GWan1234/openups/src/bms.cpp

#include "bms.h"
#include "bms_ncm.h"
#include "bms_lfp.h"
#include <Arduino.h>
#include <math.h>
#include <Preferences.h>
#include <SPIFFS.h>
#include "event_bus.h"
#include "time_utils.h"
#include "debug.h"

// 定义并初始化静态指针
BMS* BMS::instancePtr = nullptr;

BMS::BMS(I2CInterface& i2c_interface, const BMS_Config_t& config)
    : bq76920_(i2c_interface), config_(config), initialized_(false), available_(true),
      discharge_enabled_(false), charge_enabled_(false), i2c_failure_count_(0), i2c_power_enabled_(false),
      last_fast_update_(0), last_medium_update_(0), last_slow_update_(0), last_cc_update_(0),
      last_periodic_update_(0), last_day_update_(0), current_remaining_capacity(0.0f),
      accumulated_charge_mAh(0.0f), accumulated_discharge_mAh(0.0f),
      cc_ready_pending_(false), soc_initialized_(false), last_stable_soc_(50.0f),
      last_soc_update_timestamp_(0),
      soc_stable_start_time_(0), soc_waiting_for_stable_(false),
      hardware_fault_wait_(BMS_FAULT_NONE),
      full_charge_calibrated_(false),
      empty_discharge_calibrated_(false),
      last_full_charge_time_(0),
      last_empty_discharge_time_(0),
      cc_accumulated_raw_mAh_(0.0f),
      charge_soh_tracking_(false), charge_soc_start_(0.0f), charge_cc_raw_start_(0.0f),
      partial_cycles_(0.0f),
      config_update_pending_(false),
      is_quiescent_(false), quiescent_start_time_(0),
      temporary_soh_active_(false),
      pending_fet_action_(FET_ACTION_NONE) {
    
    memset(&stats_, 0, sizeof(BMS_Statistics_t));
    
    preferences_.begin(BMS_PREFS_NAMESPACE, false);
    DBG.println(F("BMS: Constructor done"));
}

BMS* BMS::create(BatteryChemistry_t chemistry, I2CInterface& i2c_interface,
                 const BMS_Config_t& config) {
    switch (chemistry) {
        case CHEM_LFP: return new BMS_LFP(i2c_interface, config);
        case CHEM_NCM:
        default:
            return new BMS_NCM(i2c_interface, config);
    }
}

BMS_Config_t BMS::getDefaultConfig(uint8_t cell_count, BatteryChemistry_t chemistry) {
    const ChemistryLimits& L = getChemistryLimits(chemistry);
    return {
        .config_version = BMS_CONFIG_VERSION,
        .cell_count = cell_count,
        .chemistry = (uint8_t)chemistry,
        .nominal_capacity_mAh = 2000,
        .cell_ov_threshold = L.recommended_ov_mV,
        .cell_uv_threshold = L.recommended_uv_mV,
        .cell_ov_recover = L.recommended_ov_rec_mV,
        .cell_uv_recover = L.recommended_uv_rec_mV,
        .max_charge_current = 2000,
        .max_discharge_current = 12000,
        .short_circuit_threshold = 20000,
        .temp_overheat_threshold = 65.0f,
        .balancing_enabled = true,
        .balancing_voltage_diff = 20.0f
    };
}

bool BMS::begin() {
    DBG.println(F("BMS: Initializing..."));
    
    // [关键] 将当前实例保存到静态变量
    instancePtr = this;
    
    if (!validateConfig(config_)) {
        DBG.println(F("BMS: Invalid config"));
        return false;
    }
    
    i2cPowerOn();
    if (!bq76920_.isConnected()) {
        DBG.println(F("BMS: BQ76920 not connected"));
        available_ = false;
        initialized_ = true;
        return true;
    }
    
    BQ76920_InitConfig chip_config = generateChipConfig(config_);
    if (!bq76920_.initializeChip(chip_config)) {
        DBG.println(F("BMS: Chip config failed"));
        available_ = false;
        return true;
    }

    loadFromStorage();

    // 学习数据化学一致性校验：SOH/剩余容量/库仑计基准/内阻均绑定具体电池组，
    // 化学切换后（无论走 Web /save、配置向导还是手改 NVS）旧数据全部失效。
    // key 缺失按 NCM 处理——LFP 支持之前的存量数据必为 NCM 组所写
    uint8_t stored_chem = preferences_.getUChar(PREFS_KEY_DATA_CHEM, (uint8_t)CHEM_NCM);
    if (stored_chem != (uint8_t)chemistry()) {
        DBG.printf_P(PSTR("BMS: stored data chemistry %u != %u, resetting battery data\n"),
            stored_chem, (uint8_t)chemistry());
        initialized_ = true;   // resetBatteryData->saveToStorage 有 initialized_ 门卫，此处临时放行
        resetBatteryData();
        initialized_ = false;
        // 换电池组后旧内阻测量结果同样失效
        memset(ir_result_mΩ_, 0, sizeof(ir_result_mΩ_));
        ir_sample_count_ = 0;
        saveIRData();
        preferences_.putUChar(PREFS_KEY_DATA_CHEM, (uint8_t)chemistry());
    }

    if (stats_.soh <= 0 || stats_.soh > 100) {
        stats_.soh = 100.0f;
        DBG.println(F("BMS: SOH reset to 100%"));
    }
    
    // 恢复之前保存的剩余容量，而不是重置为-1
    float q_max = getAvailableCapacity();
    if (current_remaining_capacity > 0 && current_remaining_capacity <= q_max) {
        DBG.printf_P(PSTR("BMS: Restored capacity: %.1f mAh (%.1f%%)\n"),
            current_remaining_capacity, (current_remaining_capacity / q_max) * 100.0f);
    } else {
        current_remaining_capacity = -1.0f;
        DBG.println(F("BMS: No valid stored capacity, will init from OCV"));
    }
    
    soc_initialized_ = false;
    
    // SOH学习上下文已在loadFromStorage()中恢复，此处不覆盖
    // updateSOHLearning()内部的current_ok和delta_soc检查会自然处理过期状态
    
    full_charge_calibrated_ = false;
    empty_discharge_calibrated_ = false;
    
    DBG.printf_P(PSTR("BMS: SOH=%.1f%%, waiting for OCV init\n"), stats_.soh);
    
 
    // [修改] 订阅事件回调
    // 使用 [] 空捕获以兼容函数指针类型
    EventBus::getInstance().subscribe(EVT_BMS_ALARM_INTERRUPT, 
        [](EventType type, void* param) {
            // 通过静态指针调用实例方法
            if (BMS::instancePtr) {
                BMS::instancePtr->handleBmsAlertInterrupt(0);
            }
        });
    initialized_ = true;
    available_ = true;
    
    bq76920_.setMOS(1, 1);
    discharge_enabled_ = true;
    charge_enabled_ = true;
    DBG.println(F("BMS: Init complete, charge/discharge enabled"));
    
    return true;
}

void BMS::update(System_Global_State& globalState) {
    if (!initialized_) return;

    unsigned long current_time = millis();
    BMS_State& bmsState = globalState.bms;
    bmsState.chemistry = (uint8_t)chemistry();
    bmsState.soc_error_est = soc_error_est_pct_;

    // 处理待更新的配置（优先执行，确保后续操作使用新配置）
    if (config_update_pending_) {
        applyPendingConfig();
    }

    if (hardware_fault_wait_ != BMS_FAULT_NONE) {
        bmsState.fault_type = hardware_fault_wait_;
        bmsState.bms_mode = BMS_MODE_FAULT;
        stats_.last_fault = hardware_fault_wait_;
        stats_.last_fault_time = getTimestamp();
        // 在 update() 阶段安全地发布故障事件，避免在 ISR 或初始化阶段触发 WDT
        EventBus::getInstance().publishInt(EVT_BMS_FAULT_DETECTED, static_cast<int>(hardware_fault_wait_));
        hardware_fault_wait_ = BMS_FAULT_NONE;
    }

    //处理万一alert中断迟滞粘连
    if (current_time - last_cc_update_ > 1000)
    {
        handleBmsAlertInterrupt(2);
    }
    
    // 真零电流窗口判定：AC在位（负载走适配器）+ 充电器已关闭 + 静置态。
    // 此时流过检流电阻的电池电流物理上为零，CC 读数即零点偏置
    cc_zero_window_ = globalState.power.ac_present &&
                      !globalState.power.charger_enabled &&
                      is_quiescent_;

    // 处理所有待处理的库仑计数据
    if (cc_ready_pending_) {
        last_cc_update_ = current_time;
        processCoulombCounterData();
    }

    if (last_fast_update_ == 0) {
        last_medium_update_ = last_slow_update_ = last_periodic_update_ = last_day_update_ = current_time;
    }

    // 预计算本轮需要执行的定时任务
    unsigned long fast_interval = is_quiescent_ ? 2000 : 500;
    unsigned long medium_interval = is_quiescent_ ? 4000 : 1000;
    unsigned long slow_interval = is_quiescent_ ? 30000 : 10000;

    bool do_fast = (current_time - last_fast_update_ >= fast_interval);
    bool do_medium = (current_time - last_medium_update_ >= medium_interval);
    bool do_slow = (current_time - last_slow_update_ >= slow_interval);
    bool do_periodic = (current_time - last_periodic_update_ >= 60000);
    bool do_day = (current_time - last_day_update_ >= 86400000);

    // ========== I2C 阶段 ==========

    // Fast: 电压、电流、温度、故障检查、静置判断
    if (do_fast) {
        bool read_success = updateBasicInfo(bmsState);

        if (read_success) {
            i2c_failure_count_ = 0;
            if (bmsState.fault_type == BMS_FAULT_CHIP_ERROR) {
                bmsState.fault_type = BMS_FAULT_NONE;
                bmsState.bms_mode = BMS_MODE_NORMAL;
            }
            bmsState.last_update_time = millis();
            checkCriticalFaults(bmsState);
            bmsState.is_connected = true;
            updateQuiescentState(bmsState);
        } else {
            handleCommunicationLoss(bmsState);
        }
        last_fast_update_ = current_time;
    }

    // Medium: 故障状态读取
    if (do_medium) {
        if (i2c_failure_count_ < 10) {
            updateFaultLogic(bmsState);
        }
    }

    // 60s轮: 读取所有寄存器 + 均衡（合并原slow的readAllRegisters到periodic）
    if (do_periodic) {
        if (i2c_failure_count_ < 10) {
            i2cPowerOn();
            bq76920_.readAllRegisters(bmsState.bq76920_registers);
            evaluateAndExecuteBalancing(bmsState);
        }
    }

    // 处理外部排队的FET操作（在I2C关闭前执行）
    processPendingFETAction();

    // 关闭 I2C（充电时保持开启以保证测量稳定）
    if (bmsState.current < 50) {
        i2cPowerOff();
    }

    // ========== 纯计算阶段 ==========

    // Medium: SOC计算、SOH跟踪、满充/放空校准检测
    if (do_medium) {
        if (i2c_failure_count_ < 10) {
            updateSOC(bmsState);
            detectChargeSOHLearning(bmsState);
            detectFullChargeCalibration(bmsState);
            detectEmptyDischargeCalibration(bmsState);
        }
        last_medium_update_ = current_time;
    }

    // Slow: SOH学习、状态解码、原始采样
    if (do_slow) {
        updateSOHLearning(bmsState);
        bmsState.soh = stats_.soh;
        bmsState.cycle_count = stats_.total_cycles;
        collectRawSample(bmsState);
        flushBurstBuffer();

        // 误差预算超限：发布校准建议（限频24h）。
        // 订阅方可提示用户/临时突破 charge_soc_stop 充到满充锚点一次
        if (soc_error_est_pct_ > 5.0f &&
            (last_calib_recommend_ms_ == 0 ||
             current_time - last_calib_recommend_ms_ >= 86400000UL)) {
            last_calib_recommend_ms_ = current_time;
            EventBus::getInstance().publish(EVT_BMS_CALIBRATION_RECOMMENDED, &soc_error_est_pct_);
            DBG.printf_P(PSTR("BMS: SOC error budget %.1f%% > 5%%, calibration charge recommended\n"),
                soc_error_est_pct_);
        }

        // 同步自消耗值到 globalState（通过外部指针访问）
        // 注意：这里只能更新 bmsState，globalState 的同步在 SystemManager 中完成

        last_slow_update_ = current_time;
    }

    // 60s轮: 均衡统计解码
    if (do_periodic) {
        bmsState.balancing_events_total = (stats_.balancing_events >> 50) & 0x3FFF;
        for (uint8_t i = 0; i < config_.cell_count && i < 5; i++) {
            uint8_t cell_shift = i * 10;
            bmsState.cell_balancing_count[i] = (stats_.balancing_events >> cell_shift) & 0x3FF;
        }
        last_periodic_update_ = current_time;
    }

    // 每天: 持久化
    if (do_day) {
        saveToStorage();
        last_day_update_ = current_time;
    }

    
}

bool BMS::disableDischarge() {
    if (!initialized_ || !available_) return false;
    pending_fet_action_ = FET_ACTION_DISABLE_DISCHARGE;
    return true;
}

bool BMS::enableDischarge() {
    if (!initialized_ || !available_) return false;
    pending_fet_action_ = FET_ACTION_ENABLE_DISCHARGE;
    return true;
}

bool BMS::disableCharge() {
    if (!initialized_ || !available_) return false;
    pending_fet_action_ = FET_ACTION_DISABLE_CHARGE;
    return true;
}

bool BMS::enableCharge() {
    if (!initialized_ || !available_) return false;
    pending_fet_action_ = FET_ACTION_ENABLE_CHARGE;
    return true;
}

bool BMS::enterShipMode() {
    if (!initialized_ || !available_) return false;
    pending_fet_action_ = FET_ACTION_ENTER_SHIP_MODE;
    return true;
}

void BMS::processAlertStatus(uint8_t fault_reg) {
    // 解析故障寄存器，仅设置标志位，不执行耗时操作
    // 所有实际处理逻辑推迟到 update() 函数中执行，避免在 ISR 或初始化阶段触发 WDT
    uint8_t real_faults = fault_reg & (~STAT_CC_READY);
    
    if (real_faults == 0 && (fault_reg & STAT_CC_READY)) {
        // 仅设置标志位，不立即处理库仑计数据
        cc_ready_pending_ = true;
        return;
    }
    
    if (real_faults != 0) {
        cc_ready_pending_ = false;
        BMS_Fault_t chip_fault = translateChipFault(real_faults);
        if (chip_fault != BMS_FAULT_NONE) {
            // 仅设置标志位，不立即发布事件
            hardware_fault_wait_ = chip_fault;
        }
    }
}

void BMS::handleBmsAlertInterrupt(uint8_t call_tag) {
    i2cPowerOn();
    uint8_t fault_reg = bq76920_.getFaultStatus();
    processAlertStatus(fault_reg);
}

void BMS::handleCommunicationLoss(BMS_State& bmsState) {
    i2c_failure_count_++;
    if (i2c_failure_count_ >= 5) {
        bmsState.fault_type = BMS_FAULT_CHIP_ERROR;
        bmsState.bms_mode = BMS_MODE_FAULT;
        stats_.last_fault = BMS_FAULT_CHIP_ERROR;
        stats_.last_fault_time = getTimestamp();
        bmsState.voltage = 0;
        bmsState.current = 0;
        bmsState.temperature = -99.0f;
        memset(bmsState.cell_voltages, 0, sizeof(bmsState.cell_voltages));
        bmsState.is_connected = false;
    }
}

// 均衡迟滞量：启动阈值 >= 10mV 时取 2mV，否则取 1mV；
// 并保证 停止阈值 = 启动阈值 - 迟滞量 恒大于 1mV。
// 目的：ADC 采集存在 1-2mV 波动，若启动/停止用同一阈值，压差在阈值附近
// 会造成隔几小时反复触发均衡的震荡
static uint16_t balancingHysteresis_mV(uint16_t start_threshold_mV) {
    uint16_t h = (start_threshold_mV >= 10) ? 2 : 1;
    if (start_threshold_mV < h + 2) {
        h = (start_threshold_mV > 2) ? (start_threshold_mV - 2) : 0;
    }
    return h;
}

bool BMS::startBalancing(BMS_State& bmsState) {
    if (!initialized_ || !config_.balancing_enabled) return false;

    bool valid_data = (bmsState.cell_voltage_max > limits().valid_cell_min_mV &&
                       bmsState.cell_voltage_max < limits().valid_cell_max_mV &&
                       bmsState.cell_voltage_min > limits().valid_cell_min_mV &&
                       bmsState.cell_voltage_min < limits().valid_cell_max_mV);
    if (!valid_data) return false;

    uint8_t balance_mask = 0;
    const uint16_t* cell_voltages = bmsState.cell_voltages;
    uint16_t start_threshold = bmsState.cell_voltage_min + (uint16_t)config_.balancing_voltage_diff;
    // 已在均衡中的电芯用更低的停止阈值判定，避免单节电芯因采样波动
    // 在 mask 中反复进出（同时避免重复累加均衡计数）
    uint16_t stop_threshold = start_threshold - balancingHysteresis_mV((uint16_t)config_.balancing_voltage_diff);

    for (uint8_t i = 0; i < config_.cell_count; i++) {
        bool already_balancing = bmsState.balance_mask & (1 << i);
        uint16_t threshold_voltage = already_balancing ? stop_threshold : start_threshold;
        bool should_balance = (cell_voltages[i] > threshold_voltage);
        if (should_balance && i > 0 && (balance_mask & (1 << (i - 1)))) {
            should_balance = false;
        }
        if (should_balance) balance_mask |= (1 << i);
    }

    if (balance_mask == 0) return false;

    i2cPowerOn();
            
    if (bq76920_.setCellBalance(balance_mask)) {
        // 只有从停止状态变为启动状态时才计数
        if (!bmsState.balancing_active) {
            unsigned long current_time = millis();
            bool should_count = false;

            if (last_balancing_stop_time_ != 0) {
                // 经历过停止，检查冷却期
                if (current_time - last_balancing_stop_time_ >= BALANCE_COUNT_INTERVAL) {
                    should_count = true;
                }
                last_balancing_stop_time_ = 0;
            } else {
                // 首次开始
                should_count = true;
            }

            if (should_count) {
                for (uint8_t i = 0; i < config_.cell_count; i++) {
                    if (balance_mask & (1 << i)) {
                        uint8_t cell_shift = i * 10;
                        uint8_t cell_count = (stats_.balancing_events >> cell_shift) & 0x3FF;
                        cell_count++;
                        int64_t clear_mask = ~(((int64_t)0x3FF) << cell_shift);
                        stats_.balancing_events &= clear_mask;
                        stats_.balancing_events |= ((int64_t)cell_count << cell_shift);
                    }
                }
                int64_t current_total = (stats_.balancing_events >> 50) & 0x3FFF;
                current_total++;
                int64_t clear_mask = ~(((int64_t)0x3FFF) << 50);
                stats_.balancing_events &= clear_mask;
                stats_.balancing_events |= (current_total << 50);
            }
        }
        // 均衡进行中mask变化：新增cell计数 + 发布事件
        else if (bmsState.balance_mask != balance_mask) {
            uint8_t added = balance_mask & ~bmsState.balance_mask;
            if (added) {
                for (uint8_t i = 0; i < config_.cell_count; i++) {
                    if (added & (1 << i)) {
                        uint8_t cell_shift = i * 10;
                        uint8_t cell_count = (stats_.balancing_events >> cell_shift) & 0x3FF;
                        cell_count++;
                        int64_t clear_mask = ~(((int64_t)0x3FF) << cell_shift);
                        stats_.balancing_events &= clear_mask;
                        stats_.balancing_events |= ((int64_t)cell_count << cell_shift);
                    }
                }
                EventBus::getInstance().publish(EVT_BMS_BALANCING_STARTED, &balance_mask);
            }
        }

        bmsState.balance_mask = balance_mask;

        if (!bmsState.balancing_active) {
            EventBus::getInstance().publish(EVT_BMS_BALANCING_STARTED, &balance_mask);
        }
        bmsState.balancing_active = true;
        return true;
    }
    return false;
}

bool BMS::stopBalancing(BMS_State& bmsState) {
    if (!initialized_) return false;
    i2cPowerOn();
    if (bq76920_.setCellBalance(0)) {
        if (bmsState.balancing_active) {
            EventBus::getInstance().publish(EVT_BMS_BALANCING_STOPPED, nullptr);
            last_balancing_stop_time_ = millis();
            bmsState.balancing_active = false;
            bmsState.balance_mask = 0;
        }
        return true;
    }
    return false;
}

void BMS::evaluateAndExecuteBalancing(BMS_State& bmsState) {
    if (!initialized_ || !config_.balancing_enabled) {
        if (initialized_) stopBalancing(bmsState);
        return;
    }

    const int16_t BALANCING_MAX_CURRENT_MA = 50;
    bool is_current_suitable = (bmsState.current >= -5 && bmsState.current <= BALANCING_MAX_CURRENT_MA);
    if (!is_current_suitable) {
        stopBalancing(bmsState);
        return;
    }

    bool valid_reading = false;
    for (uint8_t i = 0; i < config_.cell_count; i++) {
        if (bmsState.cell_voltages[i] > limits().valid_cell_min_mV &&
            bmsState.cell_voltages[i] < limits().valid_cell_max_mV) {
            valid_reading = true;
            break;
        }
    }
    if (!valid_reading) {
        stopBalancing(bmsState);
        return;
    }

    // 化学准入：LFP 仅在充电末端上升区允许均衡（平台区压差无意义）
    if (!balancingPermitted(bmsState)) {
        stopBalancing(bmsState);
        return;
    }

    // 启动/停止迟滞：启动条件 压差 >= 设定值；停止条件 压差 < 设定值 - 迟滞量。
    // 消除压差在设定值附近因 1-2mV 采样波动导致的反复启停震荡
    uint16_t voltage_diff = bmsState.cell_voltage_max - bmsState.cell_voltage_min;
    uint16_t start_diff = (uint16_t)config_.balancing_voltage_diff;
    uint16_t stop_diff = start_diff - balancingHysteresis_mV(start_diff);

    if (bmsState.balancing_active) {
        // 均衡中：压差降到停止阈值以下才停
        if (voltage_diff < stop_diff) {
            stopBalancing(bmsState);
            return;
        }
    } else {
        // 未均衡：压差达到设定值才启动
        if (voltage_diff < start_diff) {
            return;
        }
    }

    // 根据压差动态计算最低启动SOC阈值
    // 压差越大，允许的最低SOC越低（安全优先）
    float min_balancing_soc;
    if (voltage_diff >= 200) {
        min_balancing_soc = 50.0f;
    } else if (voltage_diff >= 150) {
        min_balancing_soc = 60.0f;
    } else if (voltage_diff >= 100) {
        min_balancing_soc = 65.0f;
    } else if (voltage_diff >= 50) {
        min_balancing_soc = 70.0f;
    } else {
        min_balancing_soc = 75.0f;
    }

    if (bmsState.soc < min_balancing_soc) {
        stopBalancing(bmsState);
        return;
    }

    // 启动均衡并更新状态
    if (!startBalancing(bmsState)) {
        // startBalancing失败（如无电芯需要均衡），如果之前在均衡状态则停止
        if (bmsState.balancing_active) {
            stopBalancing(bmsState);
        } else {
            bmsState.balancing_active = false;
            bmsState.balance_mask = 0;
        }
    }
}

bool BMS::clearFault() {
    if (!initialized_) return false;
    i2cPowerOn();
    return bq76920_.clearFaults(0xFF);
}

bool BMS::emergencyShutdown() {
    if (!initialized_) return false;
    pending_fet_action_ = FET_ACTION_EMERGENCY_SHUTDOWN;
    return true;
}

void BMS::processPendingFETAction() {
    PendingFETAction action = pending_fet_action_;
    if (action == FET_ACTION_NONE) return;

    pending_fet_action_ = FET_ACTION_NONE;
    i2cPowerOn();

    switch (action) {
        case FET_ACTION_DISABLE_DISCHARGE:
            bq76920_.setMOS(charge_enabled_ ? 1 : 0, 0);
            discharge_enabled_ = false;
            DBG.println(F("BMS: DFET disabled"));
            break;
        case FET_ACTION_ENABLE_DISCHARGE:
            bq76920_.setMOS(charge_enabled_ ? 1 : 0, 1);
            discharge_enabled_ = true;
            DBG.println(F("BMS: DFET enabled"));
            break;
        case FET_ACTION_DISABLE_CHARGE:
            bq76920_.setMOS(0, discharge_enabled_ ? 1 : 0);
            charge_enabled_ = false;
            DBG.println(F("BMS: CFET disabled"));
            break;
        case FET_ACTION_ENABLE_CHARGE:
            bq76920_.setMOS(1, discharge_enabled_ ? 1 : 0);
            charge_enabled_ = true;
            DBG.println(F("BMS: CFET enabled"));
            break;
        case FET_ACTION_ENTER_SHIP_MODE:
            if (bq76920_.enterShipMode()) {
                discharge_enabled_ = charge_enabled_ = false;
                DBG.println(F("BMS: Ship mode entered"));
            }
            break;
        case FET_ACTION_EMERGENCY_SHUTDOWN:
            bq76920_.setMOS(0, 0);
            discharge_enabled_ = charge_enabled_ = false;
            DBG.println(F("BMS: Emergency shutdown"));
            break;
        default:
            break;
    }
}

float BMS::getAvailableCapacity() const {
    float q_nominal = (float)config_.nominal_capacity_mAh;
    
    // Apply SOH scaling
    float q_soh = q_nominal;
    if (stats_.soh > 0 && stats_.soh <= 100) {
        q_soh = q_nominal * (stats_.soh / 100.0f);
    }
    
    // Temperature compensation (assuming we have access to temperature)
    // Note: This function is const, so we can't access bmsState directly
    // Temperature compensation will be applied in the calling context
    return q_soh;
}

float BMS::getTemperatureCompensatedCapacity(float temperature) const {
    float q_base = getAvailableCapacity();
    float k_temp = 1.0f;
    
    // Temperature compensation model based on 25°C reference
    if (temperature < 0.0f) {
        // T < 0°C: K_temp = 0.6 ~ 0.8 (linear interpolation from -20°C to 0°C)
        k_temp = 0.6f + ((temperature + 20.0f) / 20.0f) * 0.2f;
        if (k_temp < 0.6f) k_temp = 0.6f;
        if (k_temp > 0.8f) k_temp = 0.8f;
    } else if (temperature <= 25.0f) {
        // 0°C ≤ T ≤ 25°C: K_temp from 0.8 linearly rising to 1.0
        k_temp = 0.8f + (temperature / 25.0f) * 0.2f;
    } else if (temperature <= 45.0f) {
        // 25°C < T ≤ 45°C: K_temp = 1.0
        k_temp = 1.0f;
    } else {
        // T > 45°C: K_temp gradually decreases (e.g., 0.9)
        k_temp = 1.0f - ((temperature - 45.0f) / 20.0f) * 0.1f;
        if (k_temp < 0.9f) k_temp = 0.9f;
    }
    
    return q_base * k_temp;
}

void BMS::compensateSelfDischarge(unsigned long delta_time_ms) {
    if (delta_time_ms == 0) return;

    float days = (float)delta_time_ms / (1000.0f * 3600.0f * 24.0f);
    float q_max = getAvailableCapacity();

    // 使用自消耗 mA 值转换为每日百分比
    float sc_rate = self_consumption_mA_ * 24.0f / q_max;

    float loss_mah = q_max * sc_rate * days;

    current_remaining_capacity -= loss_mah;
    if (current_remaining_capacity < 0) current_remaining_capacity = 0;

    if (loss_mah > 1.0f) {
        DBG.printf_P(PSTR("BMS: Self-discharge %.2fmAh over %.2f days (rate=%.4f)\n"), loss_mah, days, sc_rate);
    }
}

// =============================================================================
// 自消耗计算 - 原始数据采集
// =============================================================================

void BMS::collectRawSample(const BMS_State& bmsState) {
    raw_call_count_++;

    uint32_t now = getTimestamp();
    if (now < 1000000000) { raw_skip_ntp_++; return; }
    if (now - last_raw_sample_time_ < 60) { raw_skip_interval_++; return; }

    RawSample& s = raw_buffer_[raw_buffer_idx_];
    s.timestamp = now;
    s.voltage_mV = bmsState.voltage;
    s.current_mA = bmsState.current;
    s.soc_pct = (uint8_t)constrain(bmsState.soc, 0.0f, 100.0f);
    s.temperature = (int8_t)constrain(bmsState.temperature, -127.0f, 127.0f);
    for (uint8_t i = 0; i < 5; i++) {
        s.cell_mv[i] = bmsState.cell_voltages[i];
    }
    // 读取库仑计原始累加值（需要 I2C，但此时可能已关闭）
    // 使用内部累积值代替，它在 processCoulombCounterData 中已维护
    s.cc_raw = (int32_t)cc_accumulated_raw_mAh_;

    raw_buffer_idx_++;
    last_raw_sample_time_ = now;

    if (raw_buffer_idx_ >= RAW_BUFFER_SIZE) {
        flushRawBuffer();
    }
}

extern SemaphoreHandle_t g_spiffs_mutex;

void BMS::flushRawBuffer() {
    raw_flush_count_++;
    if (raw_buffer_idx_ == 0) return;

    // 获取日期字符串 YYYYMMDD
    time_t now;
    time(&now);
    struct tm* tm_info = localtime(&now);
    char filename[32];
    snprintf(filename, sizeof(filename), "/raw/%04d%02d%02d.bin",
             tm_info->tm_year + 1900, tm_info->tm_mon + 1, tm_info->tm_mday);

    if (g_spiffs_mutex) xSemaphoreTake(g_spiffs_mutex, portMAX_DELAY);

    // 以追加模式写入
    File file = SPIFFS.open(filename, FILE_APPEND);
    if (!file) {
        raw_flush_fail_++;
        if (g_spiffs_mutex) xSemaphoreGive(g_spiffs_mutex);
        raw_buffer_idx_ = 0;
        return;
    }

    size_t bytes = file.write((uint8_t*)raw_buffer_, raw_buffer_idx_ * sizeof(RawSample));
    file.close();

    if (g_spiffs_mutex) xSemaphoreGive(g_spiffs_mutex);

    raw_buffer_idx_ = 0;

    // 清理超过 7 天的旧文件
    cleanupOldRawFiles();
}

void BMS::flushBurstBuffer() {
    if (burst_buffer_idx_ == 0) return;

    if (g_spiffs_mutex) xSemaphoreTake(g_spiffs_mutex, portMAX_DELAY);

    File file = SPIFFS.open("/raw/burst.bin", FILE_APPEND);
    if (!file) {
        if (g_spiffs_mutex) xSemaphoreGive(g_spiffs_mutex);
        burst_buffer_idx_ = 0;
        return;
    }

    size_t bytes = file.write((uint8_t*)burst_buffer_, burst_buffer_idx_ * sizeof(BurstSample));
    file.close();

    if (g_spiffs_mutex) xSemaphoreGive(g_spiffs_mutex);

    burst_buffer_idx_ = 0;
}

void BMS::cleanupOldRawFiles() {
    uint32_t now = getTimestamp();
    if (now < 1000000000) return;

    uint32_t cutoff = now - (30 * 86400);

    if (g_spiffs_mutex) xSemaphoreTake(g_spiffs_mutex, portMAX_DELAY);

    File root = SPIFFS.open("/raw");
    if (!root || !root.isDirectory()) {
        if (g_spiffs_mutex) xSemaphoreGive(g_spiffs_mutex);
        return;
    }

    int total = 0, removed = 0;
    File file = root.openNextFile();
    while (file) {
        const char* name = file.name();
        total++;

        // 兼容两种格式: "/raw/YYYYMMDD.bin" 或 "YYYYMMDD.bin"
        int year = 0, month = 0, day = 0;
        if (sscanf(name, "/raw/%04d%02d%02d.bin", &year, &month, &day) != 3) {
            sscanf(name, "%04d%02d%02d.bin", &year, &month, &day);
        }

        if (year > 0) {
            struct tm tm_info = {};
            tm_info.tm_year = year - 1900;
            tm_info.tm_mon = month - 1;
            tm_info.tm_mday = day;
            time_t file_time = mktime(&tm_info);

            if (file_time < (time_t)cutoff) {
                char path[32];
                snprintf(path, sizeof(path), "/raw/%04d%02d%02d.bin", year, month, day);
                SPIFFS.remove(path);
                removed++;
            }
        }
        file = root.openNextFile();
    }

    if (g_spiffs_mutex) xSemaphoreGive(g_spiffs_mutex);
}

void BMS::loadSelfConsumption() {
    self_consumption_mA_ = preferences_.getFloat(PREFS_KEY_SELF_CONSUMP, 0.83f);  // 默认20mAh/天
    sc_segment_count_ = preferences_.getUInt(PREFS_KEY_SC_SEG_COUNT, 0);
    sc_total_segments_ = preferences_.getUInt(PREFS_KEY_SC_TOTAL_SEG, 0);
    sc_last_update_ = preferences_.getUInt(PREFS_KEY_SC_LAST_UPD, 0);
    sc_last_check_ = preferences_.getUInt(PREFS_KEY_SC_LAST_CHK, 0);
}

void BMS::saveSelfConsumption() {
    preferences_.putFloat(PREFS_KEY_SELF_CONSUMP, self_consumption_mA_);
    preferences_.putUInt(PREFS_KEY_SC_SEG_COUNT, sc_segment_count_);
    preferences_.putUInt(PREFS_KEY_SC_TOTAL_SEG, sc_total_segments_);
    preferences_.putUInt(PREFS_KEY_SC_LAST_UPD, sc_last_update_);
    preferences_.putUInt(PREFS_KEY_SC_LAST_CHK, sc_last_check_);
}

void BMS::loadIRData() {
    // getBytes 需要先检查 key 是否存在
    if (preferences_.isKey(PREFS_KEY_IR_RESULT)) {
        preferences_.getBytes(PREFS_KEY_IR_RESULT, ir_result_mΩ_, sizeof(ir_result_mΩ_));
    }
    ir_sample_count_ = preferences_.getUInt(PREFS_KEY_IR_COUNT, 0);
}

void BMS::saveIRData() {
    preferences_.putBytes(PREFS_KEY_IR_RESULT, ir_result_mΩ_, sizeof(ir_result_mΩ_));
    preferences_.putUInt(PREFS_KEY_IR_COUNT, ir_sample_count_);
}

float BMS::calculateSOC_Voltage(const BMS_State& bmsState) {
    if (!initialized_ || !bq76920_.isConnected()) return -1.0f;

    uint16_t ref_cell_mv;
    if (bmsState.current > 100) {
        ref_cell_mv = bmsState.cell_voltage_max;  // 充电时：最高电压
    } else if (bmsState.current < -100) {
        ref_cell_mv = bmsState.cell_voltage_min;  // 放电时：最低电压
    } else {
        ref_cell_mv = bmsState.cell_voltage_avg;  // 静置时：平均电压
    }

    return calculateSOC_FromVoltage(ref_cell_mv);
}

float BMS::calculateSOC_FromVoltage(uint16_t voltage_mv) {
    if (voltage_mv < limits().valid_cell_min_mV ||
        voltage_mv > limits().valid_cell_max_mV) return -1.0f;
    return ocvToSoc(voltage_mv);
}

float BMS::calculateSOC_Coulomb() {
    // Note: This function doesn't have access to temperature
    // Temperature compensation is applied in updateSOC where bmsState is available
    float q_max = getAvailableCapacity();
    if (q_max <= 0) q_max = (float)config_.nominal_capacity_mAh;
    return constrain((current_remaining_capacity / q_max) * 100.0f, 0.0f, 100.0f);
}

bool BMS::applyNewConfig(const BMS_Config_t& config) {
    if (!validateConfig(config)) return false;

    // 化学类型切换必须走 重置电池数据 + 重启 流程（Web /save 负责），
    // 拒绝一切热更新旁路（MQTT/API），防止算法与实例化学不一致
    if (config.chemistry != config_.chemistry) {
        DBG.println(F("BMS: chemistry change requires restart - config rejected"));
        return false;
    }

    // 仅更新内部配置并标记需要更新硬件配置
    pending_config_ = config;
    config_update_pending_ = true;
    
    DBG.println(F("BMS: Config update marked, will apply in next update cycle"));
    return true;
}

void BMS::applyPendingConfig() {
    // 应用待更新的配置到硬件
    i2cPowerOn();
    
    // 如果芯片已连接，更新芯片配置
    if (bq76920_.isConnected()) {
        BQ76920_InitConfig chip_config = generateChipConfig(pending_config_);
        if (bq76920_.updateConfiguration(chip_config)) {
            // 硬件配置更新成功，更新内部配置并清除标记
            config_ = pending_config_;
            config_update_pending_ = false;
            DBG.println(F("BMS: Pending config applied to chip successfully"));
        } else {
            DBG.println(F("BMS: WARNING - Failed to update chip config, will retry"));
            // 注意：不清除标记，下次循环继续尝试
        }
    } else {
        DBG.println(F("BMS: WARNING - Chip not connected, config saved but not applied to chip"));
        // 芯片未连接时，仍然更新内部配置并清除标记（避免无限重试）
        config_ = pending_config_;
        config_update_pending_ = false;
    }
}

void BMS::updateSOC(BMS_State& bmsState) {
    unsigned long current_time = millis();
    unsigned long delta_ms = current_time - last_soc_update_timestamp_;

    if (last_soc_update_timestamp_ > 0) {
        compensateSelfDischarge(delta_ms);
    }
    last_soc_update_timestamp_ = current_time;

    // 温度补偿容量
    float q_max = getTemperatureCompensatedCapacity(bmsState.temperature);
    if (q_max <= 0) q_max = (float)config_.nominal_capacity_mAh;

    // 计算临时SOH并应用
    updateTemporarySOH(bmsState);
    if (stats_.soh > 0) {
        q_max = q_max * (bmsState.temporary_soh / stats_.soh);
    }

    float stable_current_threshold = config_.nominal_capacity_mAh / 20.0f;
    
    // ========== SOC 初始化 ==========
    if (!soc_initialized_) {
        DBG.println(F("BMS: SOC init starting..."));
        
        // 优先使用已恢复的存储容量
        if (current_remaining_capacity > 0 && current_remaining_capacity <= q_max) {
            last_stable_soc_ = (current_remaining_capacity / q_max) * 100.0f;
            soc_initialized_ = true;
            soc_waiting_for_stable_ = false;
            bmsState.soc = constrain(last_stable_soc_, 0.0f, 100.0f);
            DBG.printf_P(PSTR("BMS: SOC init from stored capacity: %.1f%%\n"), bmsState.soc);
            return;
        }
        
        // 电流过高时无法使用OCV，暂用50%
        if (abs(bmsState.current) > stable_current_threshold) {
            current_remaining_capacity = q_max * 0.5f;
            last_stable_soc_ = 50.0f;
            soc_initialized_ = true;
            soc_waiting_for_stable_ = true;
            soc_stable_start_time_ = current_time;
            bmsState.soc = 50.0f;
            DBG.println(F("BMS: SOC init 50% (high current, waiting for stable)"));
            return;
        }
        
        // 电流稳定，使用OCV初始化
        float soc_ocv = calculateSOC_Voltage(bmsState);
        if (soc_ocv > 0 && soc_ocv < 100) {
            current_remaining_capacity = q_max * (soc_ocv / 100.0f);
            last_stable_soc_ = soc_ocv;
            soc_waiting_for_stable_ = false;
            DBG.printf_P(PSTR("BMS: SOC init by OCV: %.1f%%\n"), soc_ocv);
        } else {
            // OCV不可用，默认50%
            current_remaining_capacity = q_max * 0.5f;
            last_stable_soc_ = 50.0f;
            soc_waiting_for_stable_ = fallbackWaitsForAnchor();  // LFP: 等锚点校准
            if (soc_waiting_for_stable_) soc_stable_start_time_ = current_time;
            DBG.println(F("BMS: SOC init default 50% (OCV unavailable)"));
        }
        
        soc_initialized_ = true;
        bmsState.soc = constrain(last_stable_soc_, 0.0f, 100.0f);
        DBG.printf_P(PSTR("BMS: SOC init done: %.1f%%\n"), bmsState.soc);
        return;
    }
    
    // ========== 等待电流稳定后用OCV重新校准 ==========
    if (soc_waiting_for_stable_) {
        if (abs(bmsState.current) <= stable_current_threshold) {
            if (current_time - soc_stable_start_time_ >= 60000) {
                float soc_ocv = calculateSOC_Voltage(bmsState);
                if (soc_ocv > 0 && soc_ocv < 100) {
                    current_remaining_capacity = q_max * (soc_ocv / 100.0f);
                    last_stable_soc_ = soc_ocv;
                    DBG.printf_P(PSTR("BMS: SOC recalibrated by OCV: %.1f%%\n"), soc_ocv);
                }
                soc_waiting_for_stable_ = false;
            }
        } else {
            soc_stable_start_time_ = current_time;
        }
    }
    
    // ========== 常规SOC计算（化学差异集中在 fuseSoc 钩子） ==========
    float soc_coulomb = (current_remaining_capacity / q_max) * 100.0f;
    fuseSoc(bmsState, soc_coulomb, q_max);

    float soc_delta = abs(bmsState.soc - last_stable_soc_);
    bmsState.soc = constrain(last_stable_soc_, 0.0f, 100.0f);
    bmsState.capacity_remaining = current_remaining_capacity;

    if (soc_delta >= 1.0f) {
        EventBus::getInstance().publish(EVT_BMS_SOC_CHANGED, &bmsState.soc);
        DBG.printf_P(PSTR("BMS: SOC %.1f%% (delta=%.1f%%)\n"), bmsState.soc, soc_delta);
    }
}

void BMS::updateSOHLearning(BMS_State& bmsState) {
    if (!restSohLearningEnabled()) return;   // LFP：静置ΔSOC法禁用（循环论证）

    float stable_current_threshold = config_.nominal_capacity_mAh / 20.0f;
    float q_nominal = (float)config_.nominal_capacity_mAh;
    float current_soc = bmsState.soc;
    
    if (!soh_learning_ctx_.is_learning) {
        // 等待开始条件：静置电流 + 合理SOC范围 + 距上次≥5分钟
        if (abs(bmsState.current) <= stable_current_threshold && 
            current_soc >= 10.0f && current_soc <= 85.0f &&
            (millis() - soh_learning_ctx_.learning_start_time > 300000)) {
            
            soh_learning_ctx_.is_learning = true;
            soh_learning_ctx_.soc_start = current_soc;
            // 记录原始库仑计累积值，而不是SOH修正后的值
            soh_learning_ctx_.ah_start = cc_accumulated_raw_mAh_;
            soh_learning_ctx_.learning_start_time = millis();
            DBG.printf_P(PSTR("BMS: SOH learning started at SOC=%.1f%%\n"), current_soc);
        }
    } else {
        // 学习进行中
        bool current_ok = (abs(bmsState.current) <= stable_current_threshold * 3);
        
        if (current_ok) {
            float delta_soc = abs(current_soc - soh_learning_ctx_.soc_start);
            
            // SOC变化≥20%才计算（低门限下库仑计误差主导，无意义）
            if (delta_soc >= 20.0f) {
                float delta_ah_raw = abs(cc_accumulated_raw_mAh_ - soh_learning_ctx_.ah_start);

                if (delta_soc > 0.1f && delta_ah_raw > 10.0f) {
                    float q_actual = delta_ah_raw / (delta_soc / 100.0f);
                    float soh_calc = (q_actual / q_nominal) * 100.0f;

                    float soh_new = 0.95f * stats_.soh + 0.05f * soh_calc;
                    soh_new = constrain(soh_new, 40.0f, 100.0f);
                    
                    DBG.printf_P(PSTR("BMS: SOH learned: dSOC=%.1f%% dAh_raw=%.1f "
                        "Q_act=%.1f SOH_calc=%.1f%% -> SOH=%.1f%%\n"),
                        delta_soc, delta_ah_raw, q_actual, soh_calc, soh_new);
                    
                    stats_.soh = soh_new;
                    bmsState.soh = stats_.soh;
                    saveToStorage();
                }
                
                soh_learning_ctx_.is_learning = false;
                soh_learning_ctx_.learning_start_time = millis();
                cc_accumulated_raw_mAh_ = 0.0f;
            }
        } else {
            soh_learning_ctx_.is_learning = false;
            soh_learning_ctx_.learning_start_time = millis();
            cc_accumulated_raw_mAh_ = 0.0f;
            DBG.println(F("BMS: SOH learning cancelled (current changed)"));
        }
    }
}

void BMS::detectFullChargeCalibration(BMS_State& bmsState) {
    float cutoff_current = config_.nominal_capacity_mAh / 20.0f;
    unsigned long current_time = millis();

    if (isFullChargeAnchor(bmsState, cutoff_current) &&
        (current_time - last_full_charge_time_ > 600000)) {

        float q_max = getTemperatureCompensatedCapacity(bmsState.temperature);
        if (q_max <= 0) q_max = (float)config_.nominal_capacity_mAh;

        // 化学相关的 SOH 结算（必须在重置 cc_accumulated_raw_mAh_ 之前）
        onFullChargeAnchor(bmsState);

        float old_soc = bmsState.soc;
        current_remaining_capacity = q_max;
        last_stable_soc_ = 100.0f;
        bmsState.soc = 100.0f;
        bmsState.capacity_remaining = current_remaining_capacity;
        full_charge_calibrated_ = true;
        last_full_charge_time_ = current_time;

        cc_accumulated_raw_mAh_ = 0.0f;
        soh_learning_ctx_.is_learning = false;
        soc_error_est_pct_ = 1.0f;   // 满充锚点：误差预算清至最小

        saveToStorage();

        DBG.printf_P(PSTR("BMS: FULL CHARGE calibration: %.1f%% -> 100%% (cap=%.1fmAh)\n"),
            old_soc, q_max);
        EventBus::getInstance().publish(EVT_BMS_SOC_CHANGED, &bmsState.soc);
    }
}

void BMS::detectEmptyDischargeCalibration(BMS_State& bmsState) {
    float cutoff_current = config_.nominal_capacity_mAh / 20.0f;
    unsigned long current_time = millis();

    if (isEmptyAnchor(bmsState, cutoff_current) &&
        (current_time - last_empty_discharge_time_ > 600000)) {

        float q_max = getTemperatureCompensatedCapacity(bmsState.temperature);
        if (q_max <= 0) q_max = (float)config_.nominal_capacity_mAh;
        float anchor_soc = emptyAnchorSoc(bmsState);   // NCM 恒 0；LFP 大电流路径 5%

        // 化学相关的 SOH 结算（在重置 cc raw 之前）
        onEmptyDischargeAnchor(bmsState);

        float old_soc = bmsState.soc;
        current_remaining_capacity = q_max * anchor_soc / 100.0f;
        last_stable_soc_ = anchor_soc;
        bmsState.soc = anchor_soc;
        bmsState.capacity_remaining = current_remaining_capacity;
        empty_discharge_calibrated_ = true;
        last_empty_discharge_time_ = current_time;

        cc_accumulated_raw_mAh_ = 0.0f;
        soh_learning_ctx_.is_learning = false;
        // 底部锚点本身有残余不确定度（IR补偿路径锚5%），清到2%而非1%
        soc_error_est_pct_ = 2.0f;

        saveToStorage();

        DBG.printf_P(PSTR("BMS: EMPTY calibration: %.1f%% -> %.1f%%\n"), old_soc, anchor_soc);
        EventBus::getInstance().publish(EVT_BMS_SOC_CHANGED, &bmsState.soc);
    }
}

void BMS::updateQuiescentState(const BMS_State& bmsState) {
    unsigned long current_time = millis();
    
    if (abs(bmsState.current) <= QUIESCENT_CURRENT_THRESHOLD) {
        // 电流在阈值内
        if (!is_quiescent_) {
            // 从活跃切换到静置，记录开始时间
            if (quiescent_start_time_ == 0) {
                quiescent_start_time_ = current_time;
            } else if (current_time - quiescent_start_time_ >= QUIESCENT_TIME_THRESHOLD) {
                // 持续10秒后进入静置状态
                is_quiescent_ = true;
                DBG.println(F("BMS: Entered quiescent state"));
            }
        }
    } else {
        // 电流超出阈值，立即切换到活跃状态
        if (is_quiescent_) {
            is_quiescent_ = false;
            quiescent_start_time_ = 0;
            DBG.printf_P(PSTR("BMS: Entered active state (current=%dmA)\n"), bmsState.current);
        } else {
            quiescent_start_time_ = 0; // 重置计时器
        }
    }
}

void BMS::checkCriticalFaults(BMS_State& bmsState) {
    BMS_Fault_t current_fault = BMS_FAULT_NONE;
    
    // cell_voltages[] 单位为 mV，有效范围（窗口按化学 limits() 取）
    uint16_t max_v = 0, min_v = UINT16_MAX;
    bool voltage_valid = false;

    for (int i = 0; i < config_.cell_count && i < 5; i++) {
        uint16_t v = bmsState.cell_voltages[i];
        if (v >= limits().valid_cell_min_mV && v <= limits().valid_cell_max_mV) {
            voltage_valid = true;
            if (v > max_v) max_v = v;
            if (v < min_v) min_v = v;
        }
    }
    
    if (bmsState.current < -(int32_t)config_.short_circuit_threshold) {
        current_fault = BMS_FAULT_SHORT_CIRCUIT;
    } else if (voltage_valid && max_v > config_.cell_ov_threshold) {
        current_fault = BMS_FAULT_OVER_VOLTAGE;
    } else if (voltage_valid && min_v < config_.cell_uv_threshold) {
        current_fault = BMS_FAULT_UNDER_VOLTAGE;
    } else if (bmsState.current > (int32_t)config_.max_charge_current || 
               bmsState.current < -(int32_t)config_.max_discharge_current) {
        current_fault = BMS_FAULT_OVER_CURRENT;
    } else if (bmsState.temperature > config_.temp_overheat_threshold) {
        current_fault = BMS_FAULT_OVER_TEMP;
    }
    
    bmsState.fault_type = current_fault;
    
    if (current_fault != BMS_FAULT_NONE) {
        bmsState.bms_mode = BMS_MODE_FAULT;
        stats_.last_fault = current_fault;
        stats_.last_fault_time = getTimestamp();
        EventBus::getInstance().publishInt(EVT_BMS_FAULT_DETECTED, static_cast<int>(current_fault));
    } else {
        bmsState.bms_mode = BMS_MODE_NORMAL;
    }
}

void BMS::updateFaultLogic(BMS_State& bmsState) {
    i2cPowerOn();
    if (!bq76920_.isConnected()) {
        bmsState.fault_type = BMS_FAULT_NONE;
        return;
    }
    
    if (bmsState.fault_type == BMS_FAULT_OVER_TEMP) return;
    
    if (bmsState.fault_type != BMS_FAULT_NONE) {
        uint8_t fault_reg = bq76920_.getFaultStatus();
        bmsState.fault_type = translateChipFault(fault_reg);
        
        if (bmsState.fault_type == BMS_FAULT_NONE) {
            bmsState.bms_mode = BMS_MODE_NORMAL;
            DBG.println(F("BMS: Fault cleared"));
        } else {
            bmsState.bms_mode = BMS_MODE_FAULT;
        }
    }
}

bool BMS::updateBasicInfo(BMS_State& bmsState) {
    bool read_success = true;
    bmsState.capacity_full = config_.nominal_capacity_mAh;

    i2cPowerOn();

    // 先读电流，判断是否发生突变（低概率，提前判断避免后续无用拷贝）
    bool burst_detected = false;
    int16_t old_current = 0;
    uint16_t old_voltage = 0;
    uint16_t old_cell_voltages[5];

    int16_t current = bq76920_.getCurrent_mA();
    if (current != -32768) {
        if (current >= -5 && current <= 5) current = 0;

        if (burst_buffer_idx_ < BURST_BUFFER_SIZE) {
            bool old_quiet = (bmsState.current == 0); //之前读取已经处理过，无需再次判断+-5
            bool new_quiet = (current == 0); // up
            int16_t burst_th = limits().burst_min_delta_mA;
            bool old_high = (bmsState.current >= burst_th || bmsState.current <= -burst_th);
            bool new_high = (current >= burst_th || current <= -burst_th);

            if ((old_quiet && new_high) || (old_high && new_quiet)) {
                burst_detected = true;
                old_current = bmsState.current;
                old_voltage = bmsState.voltage;
                for (uint8_t i = 0; i < 5; i++) old_cell_voltages[i] = bmsState.cell_voltages[i];
            }
        }

        bmsState.current = current;
        latest_current_mA_ = current;
    } else {
        read_success = false;
    }

    // 读电压
    uint16_t cell_voltages[5];
    if (bq76920_.getCellVoltages_mV(cell_voltages, config_.cell_count)) {
        for (uint8_t i = 0; i < config_.cell_count && i < 5; i++) {
            bmsState.cell_voltages[i] = cell_voltages[i];
        }

        uint32_t sum = 0;
        bmsState.cell_voltage_min = bmsState.cell_voltage_max = cell_voltages[0];

        for (uint8_t i = 0; i < config_.cell_count; i++) {
            if (cell_voltages[i] < bmsState.cell_voltage_min) bmsState.cell_voltage_min = cell_voltages[i];
            if (cell_voltages[i] > bmsState.cell_voltage_max) bmsState.cell_voltage_max = cell_voltages[i];
            sum += cell_voltages[i];
        }
        bmsState.cell_voltage_avg = sum / config_.cell_count;
        bmsState.voltage = sum;
    } else {
        read_success = false;
        uint16_t total_voltage = bq76920_.getTotalVoltage_mV();
        if (total_voltage > 9000) bmsState.voltage = total_voltage;
    }

    // 突变快照写入
    if (burst_detected && read_success) {
        BurstSample& bs = burst_buffer_[burst_buffer_idx_];
        bs.timestamp_before = getTimestamp();
        bs.timestamp_after = bs.timestamp_before;
        bs.current_before = old_current;
        bs.current_after = current;
        bs.voltage_before = old_voltage;
        bs.voltage_after = bmsState.voltage;
        for (uint8_t i = 0; i < 5; i++) {
            bs.cell_before[i] = old_cell_voltages[i];
            bs.cell_after[i] = bmsState.cell_voltages[i];
        }
        burst_buffer_idx_++;
    }

    float temp = bq76920_.getTempCelsius();
    if (temp > -98.0f && temp < 150.0f) {
        bmsState.temperature = temp;
    } else {
        read_success = false;
    }

    return read_success;
}

bool BMS::processCoulombCounterData() {
    i2cPowerOn();
    if (!initialized_ || !bq76920_.isConnected()) return false;
    if (!cc_ready_pending_) return false;

    int16_t raw_cc_value = 0;
    if (!bq76920_.readCoulombCounterRaw(raw_cc_value)) {
        DBG.println(F("BMS: CC read failed"));
        cc_ready_pending_ = false;
        return false;
    }

    bq76920_.clearCoulombCounterFlag();
    cc_ready_pending_ = false;

    unsigned long now_ms = millis();

    // ---- 零点偏置学习 ----
    // 真零窗口内原始LSB做块平均（约5分钟/块），EMA并入偏置。
    // 噪声抖动使块平均具备亚LSB分辨率；|均值|>4LSB(约6.8mA)说明窗口判定
    // 失效（有隐蔽负载），整块丢弃
    if (cc_zero_window_) {
        cc_zero_sum_lsb_ += (float)raw_cc_value;
        cc_zero_cnt_++;
        if (cc_zero_cnt_ >= CC_ZERO_BLOCK_SAMPLES) {
            float block_mean = cc_zero_sum_lsb_ / cc_zero_cnt_;
            if (fabsf(block_mean) < 4.0f) {
                cc_offset_lsb_ = 0.9f * cc_offset_lsb_ + 0.1f * block_mean;
            }
            cc_zero_sum_lsb_ = 0.0f;
            cc_zero_cnt_ = 0;
        }
    } else if (cc_zero_cnt_ > 0) {
        // 窗口中断，未满块的累积作废（避免混入非零电流样本）
        cc_zero_sum_lsb_ = 0.0f;
        cc_zero_cnt_ = 0;
    }

    // 每个LSB: 8.44μV, 积分时间250ms, 检流电阻5mΩ
    // 电荷量(mAh) = LSB * (8.44μV / 5mΩ) * (0.25s / 3600s/h) = LSB * 0.000117222
    const float CC_LSB_TO_MAH = 0.000117222f;
    float delta_mah = ((float)raw_cc_value - cc_offset_lsb_) * CC_LSB_TO_MAH;

    // ---- 丢窗补偿 ----
    // CC连续积分，寄存器只保留最近一个250ms窗，读取延迟不丢数据，
    // 但两次读取间完成了≥2个窗则中间窗被覆盖丢失（cc_ready_pending_是bool，
    // 多次中断合并为一次读取）。丢失窗数 = floor(gap/250)-1，
    // 用上一次电流读数补（电流在百ms尺度连续）。
    // 上限5s：更长的停顿说明经历了异常（如OTA前夕），不盲补
    if (last_cc_read_ms_ > 0) {
        unsigned long gap_ms = now_ms - last_cc_read_ms_;
        if (gap_ms > 500 && gap_ms <= 5000) {
            uint32_t lost_windows = (gap_ms / 250) - 1;
            float gap_mah = latest_current_mA_ * (lost_windows * 250.0f) / 3600000.0f;
            delta_mah += gap_mah;
            if (fabsf(gap_mah) > 0.05f) {
                DBG.printf_P(PSTR("BMS: CC %lu lost windows compensated %.3f mAh\n"),
                    lost_windows, gap_mah);
            }
        }
    }
    last_cc_read_ms_ = now_ms;

    current_remaining_capacity += delta_mah;
    if (delta_mah > 0) {
        accumulated_charge_mAh += delta_mah;
    } else {
        accumulated_discharge_mAh -= delta_mah;
    }

    // SOH学习用的原始累积（不受SOH缩放影响）
    cc_accumulated_raw_mAh_ += delta_mah;

    // 限制范围
    float q_max = getAvailableCapacity();
    if (q_max <= 0) q_max = (float)config_.nominal_capacity_mAh;
    current_remaining_capacity = constrain(current_remaining_capacity, 0.0f, q_max);

    // ---- 误差预算累积 ----
    // 时间项：残余偏置上界（偏置未学习时按1LSB≈1.7mA计，已学习按0.2LSB残余）
    // 吞吐项：0.5%——增益误差（检流电阻/ADC）大部分被同源SOH学习自我抵消，
    // 只计残余的二阶项
    {
        float residual_mA = (cc_offset_lsb_ == 0.0f) ? 1.7f : 0.35f;
        float err_mah = residual_mA * 0.25f / 3600.0f + fabsf(delta_mah) * 0.005f;
        soc_error_est_pct_ += (err_mah / q_max) * 100.0f;
        if (soc_error_est_pct_ > 50.0f) soc_error_est_pct_ = 50.0f;
    }

    // 循环计数（累计法：每次CC更新累加分数循环）
    accumulatePartialCycle(delta_mah);

    return true;
}

void BMS::accumulatePartialCycle(float delta_mah) {
    // 仅统计充电电量作为循环计数（充电快、放电慢，充电更能反映实际使用）
    if (delta_mah <= 0) return;

    float q_nominal = (float)config_.nominal_capacity_mAh;
    partial_cycles_ += delta_mah / q_nominal;

    while (partial_cycles_ >= 1.0f) {
        stats_.total_cycles++;
        partial_cycles_ -= 1.0f;
        DBG.printf_P(PSTR("BMS: Cycle count incremented to %u (partial=%.3f)\n"),
            stats_.total_cycles, partial_cycles_);
        saveToStorage();
    }
}

BMS_Fault_t BMS::translateChipFault(uint8_t fault_register) {
    uint8_t faults = fault_register & (~STAT_CC_READY);
    if (faults == 0) return BMS_FAULT_NONE;
    if (faults & STAT_OV) return BMS_FAULT_OVER_VOLTAGE;
    if (faults & STAT_UV) return BMS_FAULT_UNDER_VOLTAGE;
    if (faults & STAT_OCD) return BMS_FAULT_OVER_CURRENT;
    if (faults & STAT_SCD) return BMS_FAULT_SHORT_CIRCUIT;
    if (faults & STAT_DEVICE_XREADY) return BMS_FAULT_CHIP_ERROR;
    if (faults & STAT_OVRD_ALERT) return BMS_FAULT_PASSIVE_SHUTDOWN;
    return BMS_FAULT_NONE;
}

bool BMS::saveToStorage() {
    if (!initialized_) return false;
    preferences_.putFloat(PREFS_KEY_SOH, stats_.soh);
    preferences_.putUInt(PREFS_KEY_CYCLES, stats_.total_cycles);
    preferences_.putUInt(PREFS_KEY_LAST_FAULT, static_cast<uint32_t>(stats_.last_fault));
    preferences_.putUInt(PREFS_KEY_LAST_FAULT_TIME, stats_.last_fault_time);
    preferences_.putULong64(PREFS_KEY_BAL_EVENTS, stats_.balancing_events);
    
    // 保存剩余容量
    preferences_.putFloat(PREFS_KEY_REMAINING_CAP, current_remaining_capacity);
    
    // 保存累积充放电电量和SOH学习上下文
    preferences_.putFloat(PREFS_KEY_ACC_CHARGE, accumulated_charge_mAh);
    preferences_.putFloat(PREFS_KEY_ACC_DISCHARGE, accumulated_discharge_mAh);
    preferences_.putFloat(PREFS_KEY_CC_RAW_MAH, cc_accumulated_raw_mAh_);
    preferences_.putUInt(PREFS_KEY_SOH_LEARNING, soh_learning_ctx_.is_learning ? 1 : 0);
    preferences_.putFloat(PREFS_KEY_SOH_SOC_START, soh_learning_ctx_.soc_start);
    preferences_.putFloat(PREFS_KEY_SOH_AH_START, soh_learning_ctx_.ah_start);
    preferences_.putUInt(PREFS_KEY_SOH_LRN_TIME, (uint32_t)(soh_learning_ctx_.learning_start_time / 1000));
    
    // 保存循环计数分数累积和充电SOH学习状态
    preferences_.putFloat(PREFS_KEY_PARTIAL_CYCLES, partial_cycles_);
    preferences_.putUInt(PREFS_KEY_CHG_SOH_TRACK, charge_soh_tracking_ ? 1 : 0);
    preferences_.putFloat(PREFS_KEY_CHG_SOH_SOC, charge_soc_start_);
    preferences_.putFloat(PREFS_KEY_CHG_SOH_CC, charge_cc_raw_start_);

    // 保存库仑计零点偏置与误差预算
    preferences_.putFloat(PREFS_KEY_CC_OFFSET, cc_offset_lsb_);
    preferences_.putFloat(PREFS_KEY_SOC_ERR_EST, soc_error_est_pct_);
    
    DBG.printf_P(PSTR("BMS: Saved (SOH=%.1f%%, cap=%.1f mAh, acc_ch=%.1f, acc_dch=%.1f)\n"),
        stats_.soh, current_remaining_capacity, accumulated_charge_mAh, accumulated_discharge_mAh);

    // 保存自消耗计算结果
    saveSelfConsumption();

    return true;
}

bool BMS::resetBatteryData() {
    // 重置统计信息
    stats_.soh = 100.0f;
    stats_.total_cycles = 0;
    stats_.balancing_events = 0;
    stats_.last_fault = BMS_FAULT_NONE;
    stats_.last_fault_time = 0;

    // 重置容量和库仑计
    current_remaining_capacity = -1.0f;  // 触发从OCV重新初始化
    accumulated_charge_mAh = 0;
    accumulated_discharge_mAh = 0;
    cc_accumulated_raw_mAh_ = 0;

    // 重置SOC相关
    soc_initialized_ = false;  // 触发从OCV重新初始化SOC
    last_stable_soc_ = 0;

    // 重置SOH学习上下文
    soh_learning_ctx_.is_learning = false;
    soh_learning_ctx_.soc_start = 0;
    soh_learning_ctx_.ah_start = 0;
    soh_learning_ctx_.learning_start_time = 0;

    // 重置循环计数
    partial_cycles_ = 0;

    // 重置充电SOH跟踪
    charge_soh_tracking_ = false;
    charge_soc_start_ = 0;
    charge_cc_raw_start_ = 0;

    // 重置校准锚点
    full_charge_calibrated_ = false;
    empty_discharge_calibrated_ = false;

    // 重置临时SOH迟滞状态
    temporary_soh_active_ = false;

    // 误差预算重置为高不确定度（新电池组一无所知）；
    // cc_offset_lsb_ 是板级属性（检流电阻+AFE失调），换电池组不重置
    soc_error_est_pct_ = 10.0f;
    cc_zero_sum_lsb_ = 0.0f;
    cc_zero_cnt_ = 0;

    // 持久化到NVS
    bool result = saveToStorage();

    DBG.println(F("[BMS] 电池数据已重置"));
    return result;
}

bool BMS::loadFromStorage() {
    stats_.soh = preferences_.getFloat(PREFS_KEY_SOH, 100.0f);
    stats_.total_cycles = preferences_.getUInt(PREFS_KEY_CYCLES, 0);
    stats_.last_fault = static_cast<BMS_Fault_t>(preferences_.getUInt(PREFS_KEY_LAST_FAULT, 0));
    stats_.last_fault_time = preferences_.getUInt(PREFS_KEY_LAST_FAULT_TIME, 0);
    stats_.balancing_events = preferences_.getULong64(PREFS_KEY_BAL_EVENTS, 0);
    
    // 恢复剩余容量
    current_remaining_capacity = preferences_.getFloat(PREFS_KEY_REMAINING_CAP, -1.0f);
    
    // 恢复累积充放电电量和SOH学习上下文
    accumulated_charge_mAh = preferences_.getFloat(PREFS_KEY_ACC_CHARGE, 0.0f);
    accumulated_discharge_mAh = preferences_.getFloat(PREFS_KEY_ACC_DISCHARGE, 0.0f);
    cc_accumulated_raw_mAh_ = preferences_.getFloat(PREFS_KEY_CC_RAW_MAH, 0.0f);
    soh_learning_ctx_.is_learning = preferences_.getUInt(PREFS_KEY_SOH_LEARNING, 0) != 0;
    soh_learning_ctx_.soc_start = preferences_.getFloat(PREFS_KEY_SOH_SOC_START, 0.0f);
    soh_learning_ctx_.ah_start = preferences_.getFloat(PREFS_KEY_SOH_AH_START, 0.0f);
    soh_learning_ctx_.learning_start_time = (unsigned long)preferences_.getUInt(PREFS_KEY_SOH_LRN_TIME, 0) * 1000UL;
    
    // 恢复循环计数分数累积和充电SOH学习状态
    partial_cycles_ = preferences_.getFloat(PREFS_KEY_PARTIAL_CYCLES, 0.0f);
    charge_soh_tracking_ = preferences_.getUInt(PREFS_KEY_CHG_SOH_TRACK, 0) != 0;
    charge_soc_start_ = preferences_.getFloat(PREFS_KEY_CHG_SOH_SOC, 0.0f);
    charge_cc_raw_start_ = preferences_.getFloat(PREFS_KEY_CHG_SOH_CC, 0.0f);

    // 恢复库仑计零点偏置与误差预算（重启期间未计数，起始误差加0.5%保守量）
    cc_offset_lsb_ = preferences_.getFloat(PREFS_KEY_CC_OFFSET, 0.0f);
    if (fabsf(cc_offset_lsb_) > 10.0f) cc_offset_lsb_ = 0.0f;   // 异常值防御
    soc_error_est_pct_ = preferences_.getFloat(PREFS_KEY_SOC_ERR_EST, 5.0f) + 0.5f;
    soc_error_est_pct_ = constrain(soc_error_est_pct_, 0.0f, 50.0f);
    
    if (stats_.soh < 0 || stats_.soh > 100) stats_.soh = 100.0f;

    // 恢复自消耗计算结果
    loadSelfConsumption();

    // 恢复内阻估算结果
    loadIRData();

    return true;
}

bool BMS::validateConfig(const BMS_Config_t& config) {
    if (config.cell_count < 3 || config.cell_count > 5) return false;  // 硬件仅支持3-5串，与ConfigManager保持一致
    if (config.nominal_capacity_mAh == 0) return false;
    if (config.cell_ov_threshold <= config.cell_uv_threshold) return false;
    if (config.chemistry > CHEM_LFP) return false;
    return true;
}

BQ76920_InitConfig BMS::generateChipConfig(const BMS_Config_t& config) {
    return {
        .cell_count = config.cell_count,
        .cell_ov_threshold = config.cell_ov_threshold,
        .cell_uv_threshold = config.cell_uv_threshold,
        .ov_delay = OV_DELAY_1_S,
        .uv_delay = UV_DELAY_1_S,
        .max_discharge_current = config.max_discharge_current,
        .ocd_delay = OCD_DELAY_80_MS,
        .short_circuit_threshold = config.short_circuit_threshold,
        .scd_delay = SCD_DELAY_100_US,
        .coulomb_counter_enabled = true
    };
}

// =============================================================================
// 化学常量边界表（与 battery_chemistry.h 配套；数值依据见 docs/lfp-bms-inheritance-plan.md）
// =============================================================================
static const ChemistryLimits CHEM_LIMITS_NCM = {
    .valid_cell_min_mV = 2500, .valid_cell_max_mV = 4500,
    .ov_range_min_mV = 4000, .ov_range_max_mV = 4500,
    .ov_rec_min_mV   = 4000, .ov_rec_max_mV   = 4300,
    .uv_range_min_mV = 2500, .uv_range_max_mV = 3500,
    .uv_rec_min_mV   = 2800, .uv_rec_max_mV   = 3300,
    .recommended_ov_mV = 4210, .recommended_ov_rec_mV = 4180,
    .recommended_uv_mV = 3000, .recommended_uv_rec_mV = 3050,
    .recommended_charge_cell_mV = 4150,   // 4200 会违反 充电电压<=串数*(OV-30) 交叉校验，取保守值
    .nominal_cell_mV = 3700,
    .burst_min_delta_mA = 1000,
    .name = "NCM",
};
static const ChemistryLimits CHEM_LIMITS_LFP = {
    .valid_cell_min_mV = 2000, .valid_cell_max_mV = 4000,
    .ov_range_min_mV = 3500, .ov_range_max_mV = 3800,
    .ov_rec_min_mV   = 3400, .ov_rec_max_mV   = 3600,
    .uv_range_min_mV = 2000, .uv_range_max_mV = 2900,
    .uv_rec_min_mV   = 2300, .uv_rec_max_mV   = 3000,
    .recommended_ov_mV = 3650, .recommended_ov_rec_mV = 3550,
    .recommended_uv_mV = 2500, .recommended_uv_rec_mV = 2800,
    .recommended_charge_cell_mV = 3600,
    .nominal_cell_mV = 3200,
    .burst_min_delta_mA = 2000,
    .name = "LiFePO4",
};

const ChemistryLimits& getChemistryLimits(BatteryChemistry_t chem) {
    return (chem == CHEM_LFP) ? CHEM_LIMITS_LFP : CHEM_LIMITS_NCM;
}
