GWan1234/openups/src/i18n_strings_en.h

#ifndef I18N_STRINGS_EN_H
#define I18N_STRINGS_EN_H

#include "i18n.h"

// =============================================================================
// English String Table
// =============================================================================

// Common
static const char s_en_0[] PROGMEM = "Enabled";
static const char s_en_1[] PROGMEM = "Disabled";

// addTip time format
static const char s_en_2[] PROGMEM = "[%02d/%02d %02d:%02d]";

// addTip messages: state transitions
static const char s_en_3[] PROGMEM = "BMS offline, entering CRITICAL";
static const char s_en_4[] PROGMEM = "BQ24780S offline, entering CRITICAL";
static const char s_en_5[] PROGMEM = "BMS fault(%d), entering CRITICAL";
static const char s_en_6[] PROGMEM = "System entering CRITICAL";
static const char s_en_7[] PROGMEM = "Power fault(%d), entering WARNING";
static const char s_en_8[] PROGMEM = "Over-current triggered, entering WARNING";
static const char s_en_9[] PROGMEM = "Over-temp triggered, entering WARNING";
static const char s_en_10[] PROGMEM = "BQ24780S register mismatch, entering WARNING";
static const char s_en_11[] PROGMEM = "BQ76920 register mismatch, entering WARNING";
static const char s_en_12[] PROGMEM = "System entering WARNING";

// addTip messages: BMS faults
static const char s_en_13[] PROGMEM = "BMS over-temp: disable charge/discharge";
static const char s_en_14[] PROGMEM = "BMS over-voltage: disable charge";
static const char s_en_15[] PROGMEM = "BMS under-voltage: disable discharge";
static const char s_en_16[] PROGMEM = "BMS over-current: disable charge/discharge";
static const char s_en_17[] PROGMEM = "BMS short-circuit: emergency shutdown";
static const char s_en_18[] PROGMEM = "BMS chip error";
static const char s_en_19[] PROGMEM = "BMS passive shutdown: disable charge/discharge";
static const char s_en_20[] PROGMEM = "BMS unknown fault(%d)";

// addTip messages: register mismatch
static const char s_en_21[] PROGMEM = "mismatch: reg=%dmA, cfg=%dmA";
static const char s_en_22[] PROGMEM = "mismatch: reg=%dmV, cfg=%dmV";

// addTip messages: battery operations
static const char s_en_23[] PROGMEM = "Battery data reset (SOH/cycles/balancing)";

// addTip messages: charge/discharge events
static const char s_en_24[] PROGMEM = "Charging, SOC:%.1f%%, current:%dmA, voltage:%dmV";
static const char s_en_25[] PROGMEM = "Charge stopped, SOC:%.1f%%";
static const char s_en_26[] PROGMEM = "Balancing started, SOC:%.1f%%, cells: %s";
static const char s_en_27[] PROGMEM = "Balancing stopped, SOC:%.1f%%";

// MQTT entity names
static const char s_en_28[] PROGMEM = "Battery SOC";
static const char s_en_29[] PROGMEM = "Battery SOH";
static const char s_en_30[] PROGMEM = "Battery Voltage";
static const char s_en_31[] PROGMEM = "Battery Current";
static const char s_en_32[] PROGMEM = "Battery Temperature";
static const char s_en_33[] PROGMEM = "Battery Capacity Remaining";
static const char s_en_34[] PROGMEM = "Battery Cycle Count";
static const char s_en_35[] PROGMEM = "Self Consumption Current";
static const char s_en_36[] PROGMEM = "Cell %d Voltage";
static const char s_en_37[] PROGMEM = "Cell Min Voltage";
static const char s_en_38[] PROGMEM = "Cell Max Voltage";
static const char s_en_39[] PROGMEM = "Cell Avg Voltage";
static const char s_en_40[] PROGMEM = "Input Voltage";
static const char s_en_41[] PROGMEM = "Input Current";
static const char s_en_42[] PROGMEM = "Output Power";
static const char s_en_43[] PROGMEM = "Battery Voltage(adc)";
static const char s_en_44[] PROGMEM = "Battery Current(adc)";
static const char s_en_45[] PROGMEM = "AC Power";
static const char s_en_46[] PROGMEM = "Charger Enabled";
static const char s_en_47[] PROGMEM = "Balancing Active";
static const char s_en_48[] PROGMEM = "WiFi Connected";
static const char s_en_49[] PROGMEM = "BMS Fault";
static const char s_en_50[] PROGMEM = "Power Fault";
static const char s_en_51[] PROGMEM = "Emergency Shutdown";
static const char s_en_52[] PROGMEM = "Over Current Protection";
static const char s_en_53[] PROGMEM = "Over Temperature Protection";
static const char s_en_54[] PROGMEM = "Short Circuit Protection";
static const char s_en_55[] PROGMEM = "System Uptime";
static const char s_en_56[] PROGMEM = "Board Temperature";
static const char s_en_57[] PROGMEM = "Environment Temperature";
static const char s_en_58[] PROGMEM = "SHTC3 Temperature";
static const char s_en_59[] PROGMEM = "SHTC3 Humidity";
static const char s_en_60[] PROGMEM = "WiFi RSSI";
static const char s_en_61[] PROGMEM = "Firmware Version";
static const char s_en_62[] PROGMEM = "Power Mode";
static const char s_en_63[] PROGMEM = "Overall Status";
static const char s_en_64[] PROGMEM = "WiFi SSID";
static const char s_en_65[] PROGMEM = "LED Brightness";
static const char s_en_66[] PROGMEM = "Buzzer Volume";
static const char s_en_67[] PROGMEM = "HID Report Mode";
static const char s_en_68[] PROGMEM = "Cell %d Internal Resistance";
static const char s_en_69[] PROGMEM = "IR Sample Count";
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
